RocketManRC/EMMMA-K-V3-M/STL-Files/CoverThin-LowerPlate-EMMMA-K-v3.2.png

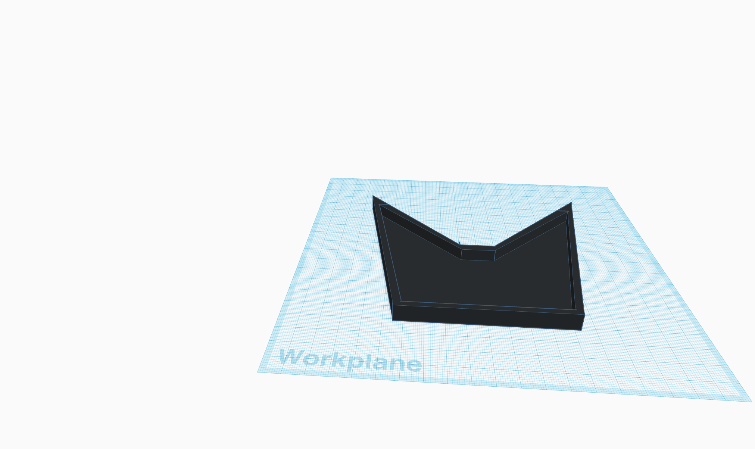
STL-Files/CoverThin-LowerPlate-EMMMA-K-v3.2.png
