RocketManRC/EMMMA-K-V3-M/STL-Files/EMMMA-K-v3-pin-spacers-24.png

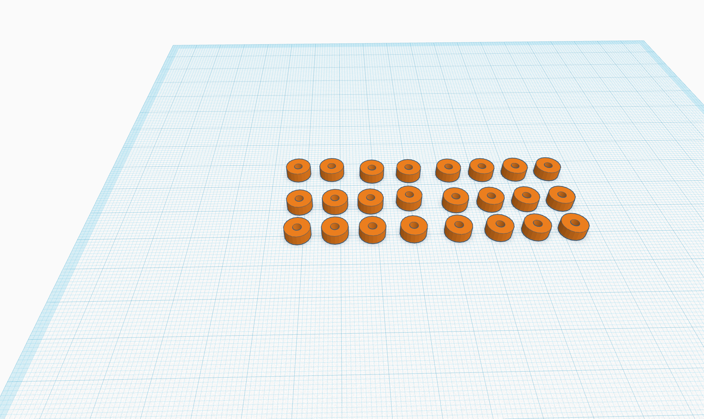
STL-Files/EMMMA-K-v3-pin-spacers-24.png
