RocketManRC/EMMMA-K-V3-M/STL-Files/EMMMA-K-v3.2.png

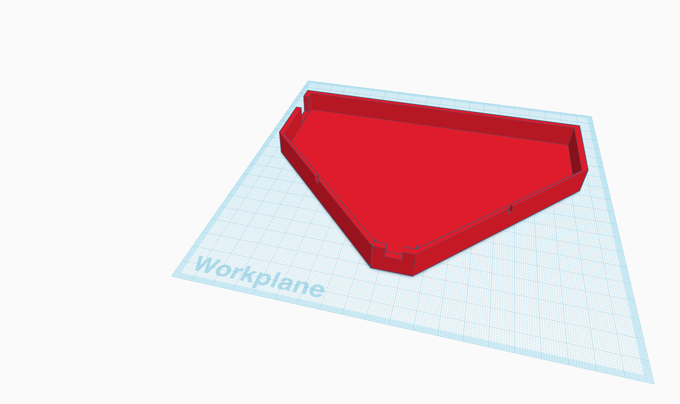
STL-Files/EMMMA-K-v3.2.png
