RocketManRC/EMMMA-K-V3-M/STL-Files/Hex-spacer-holder-bottom.png

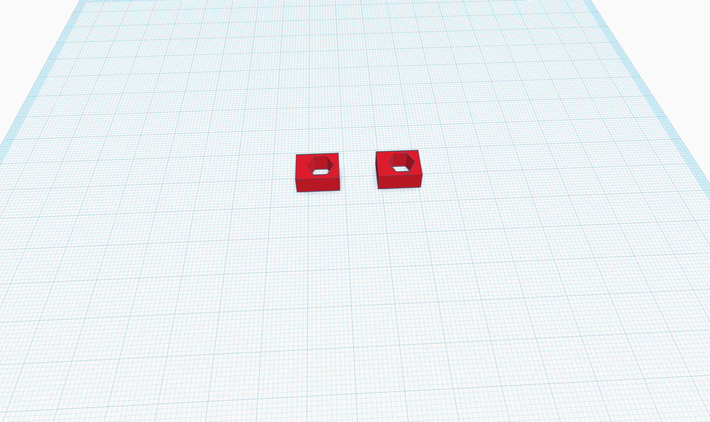
STL-Files/Hex-spacer-holder-bottom.png
