RocketManRC/EMMMA-K-V3-M/STL-Files/Hex-spacer-holder.png

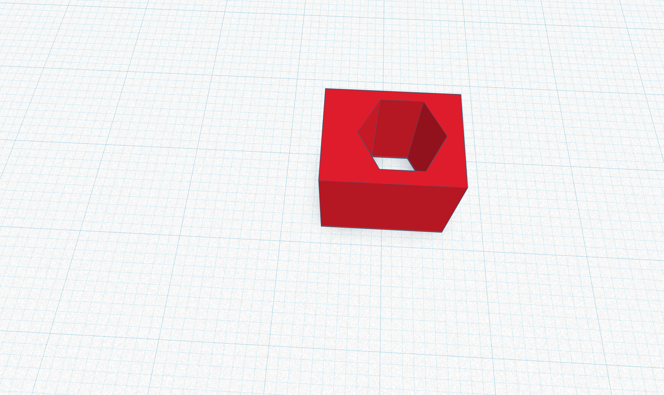
STL-Files/Hex-spacer-holder.png
