RocketManRC/EMMMA-K-V3-M/STL-Files/LowerPlate-EMMMA-K-v3.2.png

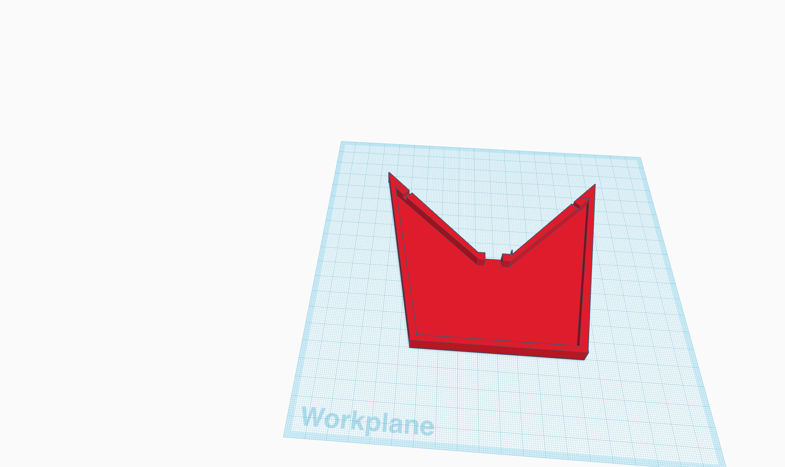
STL-Files/LowerPlate-EMMMA-K-v3.2.png
