RocketManRC/EMMMA-K-V3-M/STL-Files/USB-C-AdapterPlateEMMMA-K-v3.png

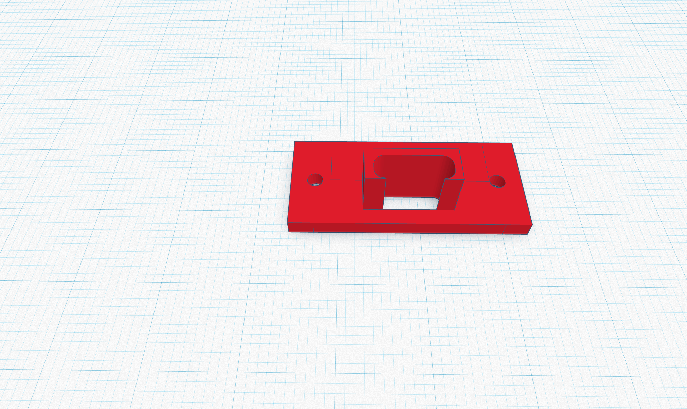
STL-Files/USB-C-AdapterPlateEMMMA-K-v3.png
